borisnimcevic/Broys/hardware/kicad-parts/USBC-USB4105-GF-A/USB4105-GF-A.step

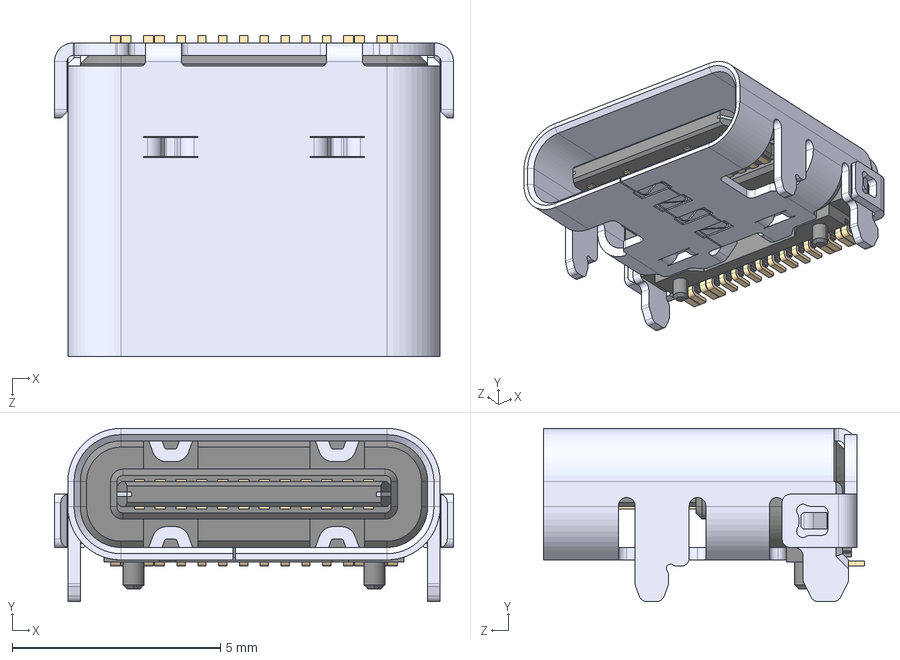
[picture p15: CAD file, 2022-06-16]
hardware/kicad-parts/USBC-USB4105-GF-A/USB4105-GF-A.step
9.58 x 4.16 x 7.71 mm
