borisnimcevic/Broys/hardware/kicad-parts/battery_charger-MCP73832T/MCP73832T-2DCI_OT.step

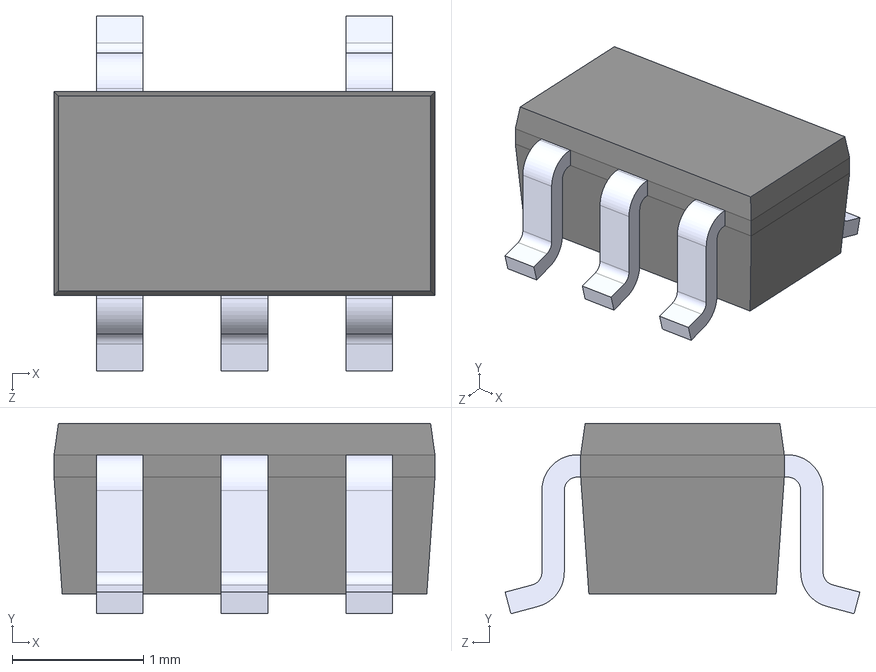
[picture p16: CAD file, 2022-07-06]
hardware/kicad-parts/battery_charger-MCP73832T/MCP73832T-2DCI_OT.step
2.90 x 1.45 x 2.70 mm
