borisnimcevic/Broys/hardware/kicad-parts/battery_connector-665102131822/665102131822.step

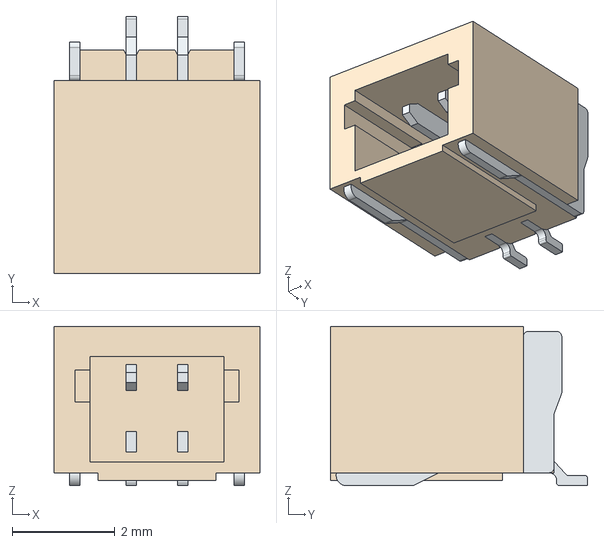
[picture p17: CAD file, 2022-07-06]
hardware/kicad-parts/battery_connector-665102131822/665102131822.step
4.00 x 5.00 x 3.10 mm
